szymonkaliski/nott/ui/consts.py

from enum import Enum


CHUCK_HOST = "127.0.0.1"
CHUCK_IN_PORT = 3001
CHUCK_OUT_PORT = 3000

LOOPS_COUNT = 6
RATES = [0.125, 0.25, 0.5, 1.0, 2.0, 4.0, 8.0]


class COLOR(object):
    OFF = 0
    WHITE_MUTED = 50
    WHITE = 255


class MODE(Enum):
    PLAY = 1
    CONTROL_1 = 2
    CONTROL_2 = 3
    CONTROL_3 = 4


class PLAYBACK_MODES(object):
    STANDARD = "MODE_STANDARD"
    GRANULAR = "MODE_GRANULAR"
